cy-rhino/StrayCAT/misc/StrayCAT_Slave/StrayCAT_Custom.h

/*
 *  Header file for EasyCAT library
 *
 *  This file has been created by the StrayCAT ESI Tool.
 */

#ifndef CUSTOM_PDO_NAME_H
#define CUSTOM_PDO_NAME_H

#define CUST_BYTE_NUM_OUT 1
#define CUST_BYTE_NUM_IN  8
#define TOT_BYTE_NUM_ROUND_OUT 4
#define TOT_BYTE_NUM_ROUND_IN  8

// output buffer
typedef union
{
  uint8_t Byte [TOT_BYTE_NUM_ROUND_OUT];
  struct
  {
    uint8_t Leds;
  } Cust;
} PROCBUFFER_OUT;

// input buffer
typedef union
{
  uint8_t Byte [TOT_BYTE_NUM_ROUND_IN];
  struct
  {
    uint16_t Analog_0;
    uint16_t Analog_1;
    uint16_t Bit16_RisingRamp;
    uint8_t DipSwitches;
    uint8_t Bit8_FallingRamp;
  } Cust;
} PROCBUFFER_IN;

#endif
